someyob/Pico-16C/pics/20221012_140322.jpg

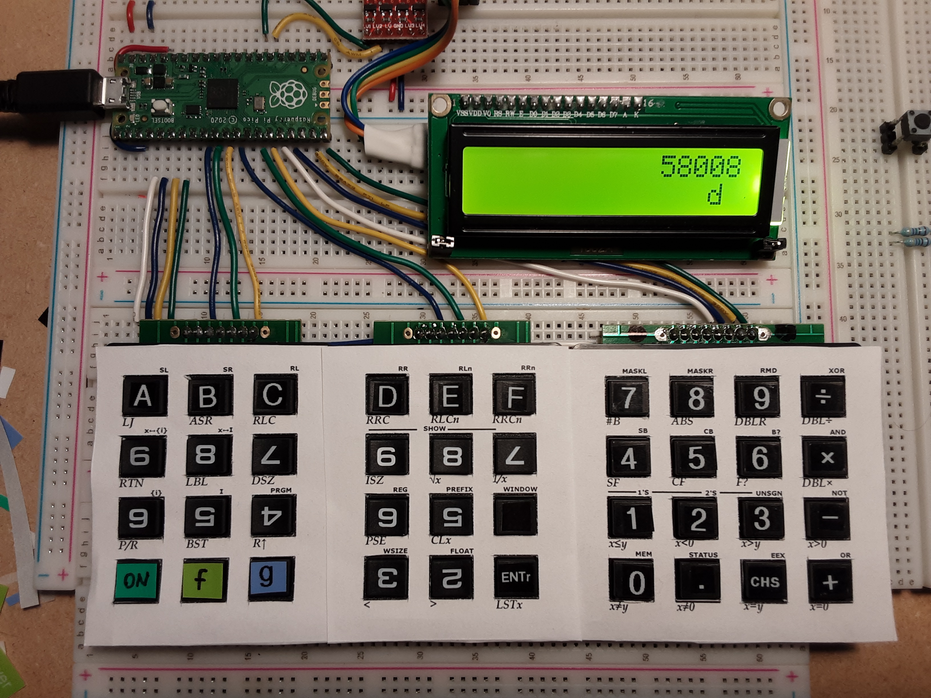
pics/20221012_140322.jpg
