someyob/Pico-16C/pics/20221012_140349.jpg

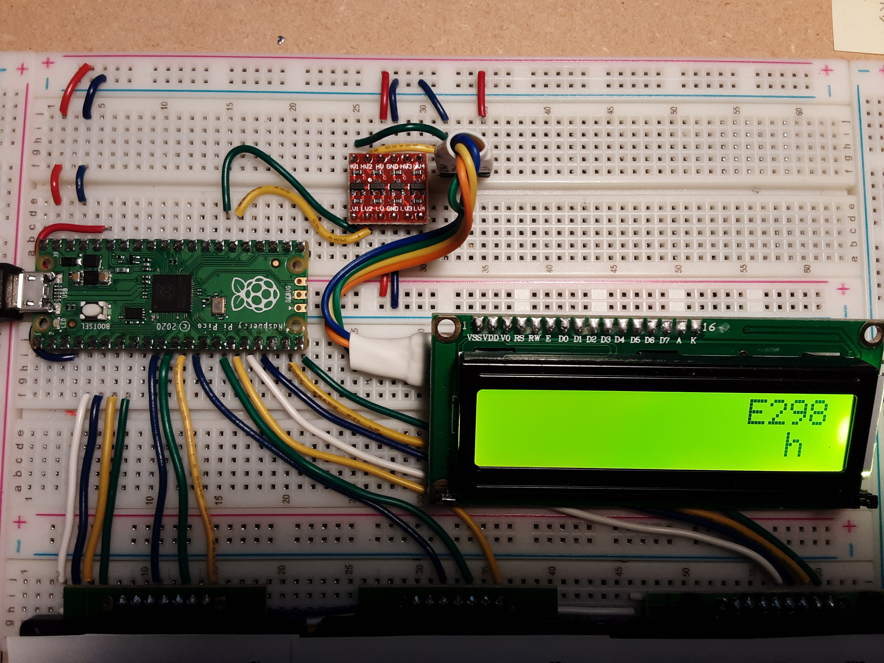
pics/20221012_140349.jpg
