someyob/Pico-16C/pics/20221128_145956.jpg

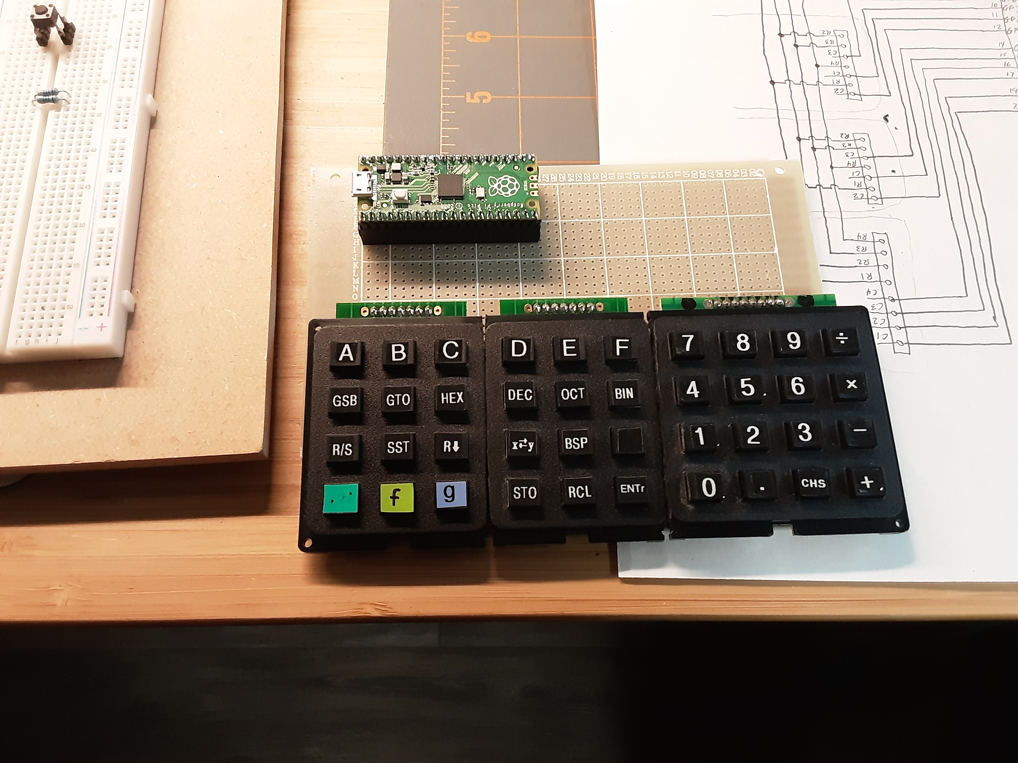
pics/20221128_145956.jpg
