someyob/Pico-16C/pics/20221128_160009.jpg

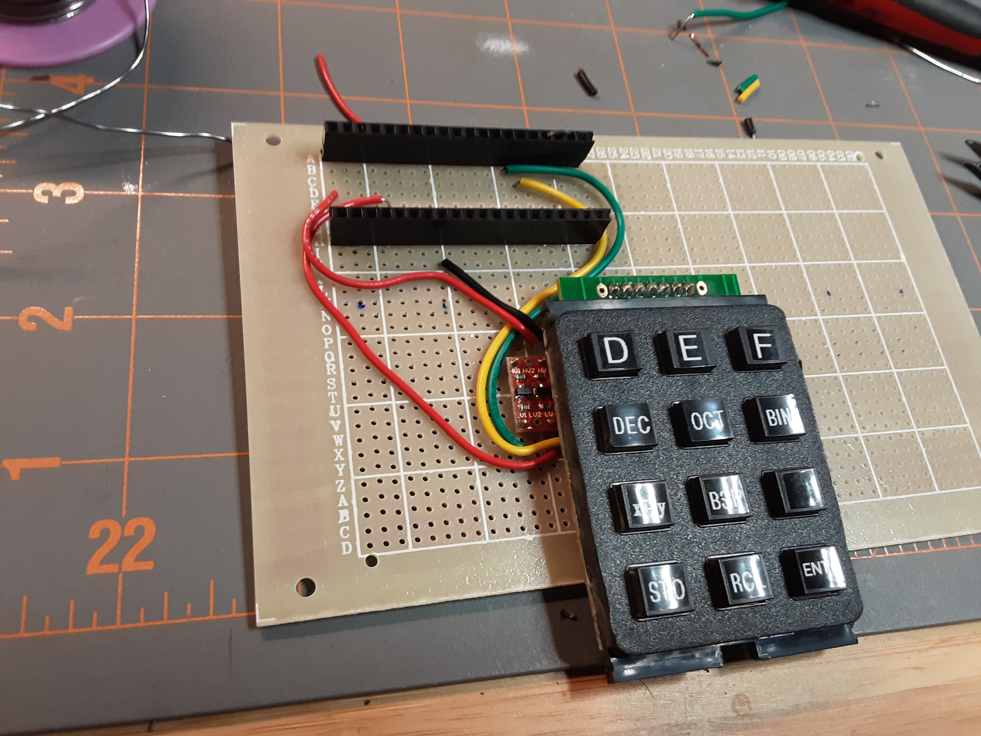
pics/20221128_160009.jpg
