someyob/Pico-16C/pics/20221128_160430.jpg

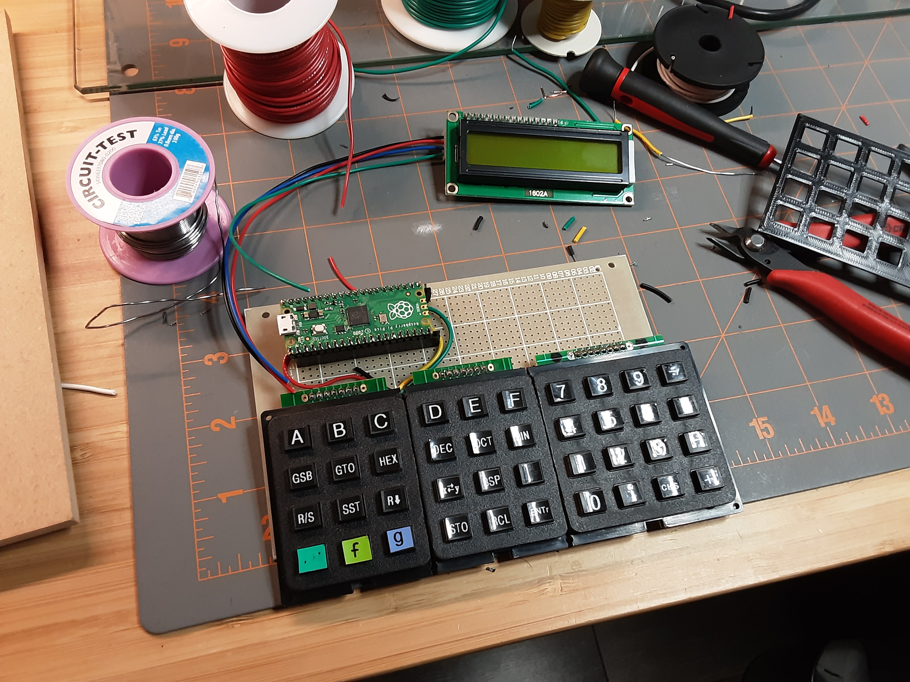
pics/20221128_160430.jpg
