someyob/Pico-16C/pics/20221129_114137.jpg

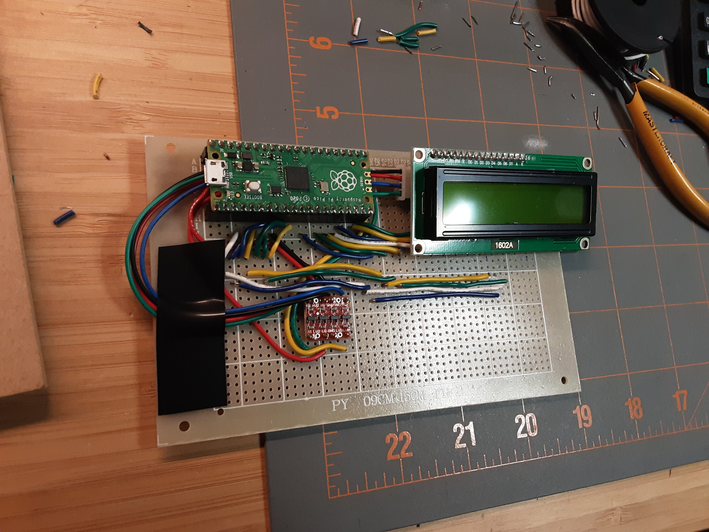
pics/20221129_114137.jpg
