someyob/Pico-16C/pics/20221216_111910.jpg

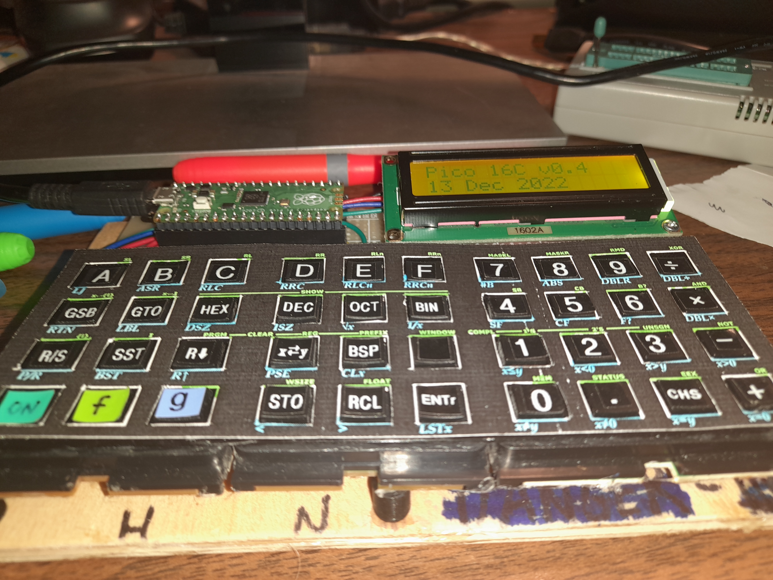
pics/20221216_111910.jpg
