someyob/Pico-16C/pics/20221216_111938.jpg

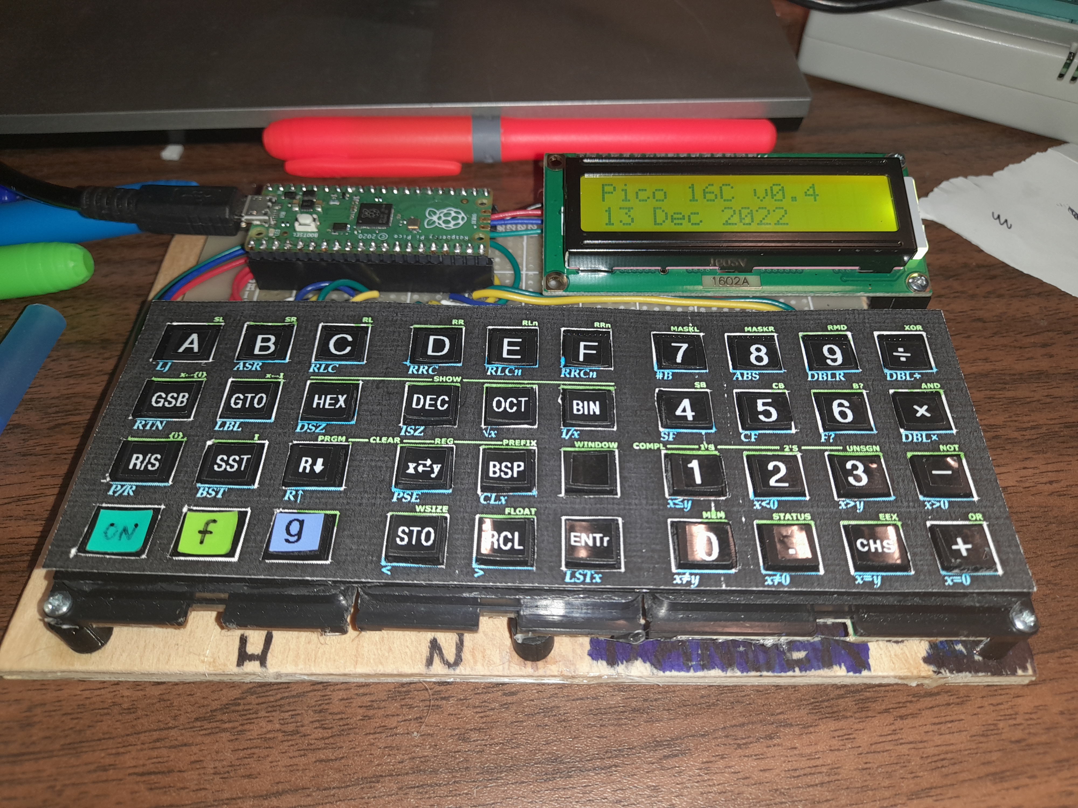
pics/20221216_111938.jpg
